str4el/homelogic/firmware/bus.c

/*
 * Copyright (C) 2013, 2014 Stephan Reinhard <Stephan-Reinhard@gmx.de>
 *
 * This file is part of Homelogic.
 *
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
 * You should have received a copy of the GNU General Public License
 * along with Homelogic.  If not, see <http://www.gnu.org/licenses/>.
 */

#include <ctype.h>
#include <string.h>
#include <stdio.h>
#include <stdlib.h>
#include <stdarg.h>
#include <stdbool.h>
#include <avr/eeprom.h>
#include <util/atomic.h>

#include "bus.h"
#include "usb.h"
#include "main.h"
#include "rtc.h"
#include "memory.h"
#include "prog.h"
#include "../common/timer.h"
#include "../common/counter.h"




bus_t bus = {
        .status = rx_start,

        .rx_buffer = "",
        .rx_len = 0,

        .tx_lock = 0,
        .tx_list = NULL,
};




const bus_command_table_t bus_command_table [] PROGMEM = {
        { "RESET", 5, bus_command_reset,          0,  0},
        { "IDY"  , 3, bus_command_identify,       0,  0},
        { "RUN"  , 3, bus_command_run,            0,  0},
        { "STOP" , 4, bus_command_stop,           0,  0},
        { "DEBUG", 5, bus_command_debug,          0,  0},
        { "STEP" , 4, bus_command_step,           0,  0},
        { "DUMP" , 4, bus_command_dump,           0,  0},
        { "PROG" , 4, bus_command_program,        8, BUS_DATA_MAX_LEN},
#ifdef RTC_SUPPORT
        { "SRTC" , 4, bus_command_set_rtc,       20, 20},
#endif
        { "SET"  , 3, bus_command_set_word,       8, 15},
        { "MEM"  , 3, bus_command_memory,         0,  0},
};





ISR(BUS_RXC_vect) {
        uint8_t in = BUS_UDR;

        switch (bus.status) {
        case rx_start:
                bus.rx_len = 0;
                bus.status = rx_ready;
        case rx_ready:
                if (bus.rx_len < BUS_BUFSIZE - 1) {
                        bus.rx_buffer[bus.rx_len] = in;
                        bus.rx_len++;
                }


                if (in == '\r') {
#ifdef USB_SUPPORT
                        usb_send_data(bus.rx_buffer, bus.rx_len);
#endif
                        bus.rx_buffer[bus.rx_len] = 0;
                        bus_command(bus.rx_buffer);
                        bus.rx_len = 0;
                }

                BUS_TX_LOCK(2 + adr * 2);
                break;

        case tx_start:
                bus.rx_len = 0;
                bus.status = tx_verify;
        case tx_verify:
                if (bus.rx_len < BUS_BUFSIZE) {
                        bus.rx_buffer[bus.rx_len] = in;
                        bus.rx_len++;
                }
                break;

        default:
                BUS_TX_LOCK(2 + adr * 2);
        }

}




void bus_init(void)
{
        ATOMIC_BLOCK(ATOMIC_RESTORESTATE) {
                SFR_SET(BUS_UCSZ0);
                SFR_SET(BUS_UCSZ1);
                SFR_SET(BUS_TXEN);
                SFR_SET(BUS_RXEN);
                SFR_SET(BUS_RXCIE);

                /* Aus einem mir absuolut räzelhaftem Grund funktioniert das Einstellen
                 * der Baudrate beim AtMega32 nur wenn es nach dem setzen der Flags passiert!
                 */
                BUS_UBRRH = UBRRH_VALUE;
                BUS_UBRRL = UBRRL_VALUE;
#if USE_2X
                SFR_SET(BUS_U2X);
#else
                SFR_CLR(BUS_U2X);
#endif
        }

        PIN_CLR(RE);
        BUS_TX_LOCK(2 + adr * 2);
}




void bus_transmit_data (const char * data, uint8_t len)
{
#ifdef USB_SUPPORT
        usb_send_data(data, (uint16_t) len);
#endif

        while (bus.tx_lock);
        bus.status = tx_start;
        PIN_SET(TE);


        for (uint8_t i = 0; i < len; i++) {
                while(SFR_IS_LOW(BUS_UDRE));
                BUS_UDR = data[i];
        }

        while (SFR_IS_LOW(BUS_TXC));
        SFR_SET(BUS_TXC);

        PIN_CLR(TE);
        BUS_TX_LOCK(2 + adr * 2);
        bus.status = rx_start;
}




bool bus_send_raw_sync(const char *data, uint8_t len)
{
        uint8_t count = 0;
        bus_transmit_data(data, len);
        while (!(len == bus.rx_len && memcmp(data, bus.rx_buffer, len) == 0)) {
                if (++count > BUS_MAX_RETRY) return false;
                bus_transmit_data(data, len);
        }
        return true;
}




bool bus_send_raw_async(const char *data, uint8_t len)
{
        bus_data_list_t *new = malloc(sizeof(*new) + len);
        if (!new) return false;

        new->next = NULL;
        new->len = len;
        memcpy(&new->data, data, len);

        if (bus.tx_list) {
                bus_data_list_t *last = bus.tx_list;
                while (last->next) last = last->next;
                last->next = new;
        } else {
                bus.tx_list = new;
        }

        return true;
}




void bus_flush_send_buffer()
{
        while (bus.tx_list) {
                bus_data_list_t *next = bus.tx_list->next;
                bus_send_raw_sync(&bus.tx_list->data, bus.tx_list->len);
                free(bus.tx_list);
                bus.tx_list = next;
        }
}




/* Erstellt eine Mitteilung im Standardformat und kopiert sie in den Sendepuffer
 */
bool bus_send_message_async(const char *cmd, uint8_t dst, const char *format, ...)
{
        char str[BUS_BUFSIZE];
        uint8_t len;

        len = snprintf(str, sizeof(str), "%s %02X %02X ", cmd, adr, dst);
        if (len >= sizeof(str) - 1) return false;

        if (format) {
                va_list args;
                va_start(args, format);
                len += vsnprintf(str + len, sizeof(str) - len, format, args);
                va_end(args);
                if (len >= sizeof(str) - 1) return false;
        }

        str[len] = '\r';
        return bus_send_raw_async(str, len + 1);
}




/* Erstellt eine Mitteilung im Standardformat und versendet sie
 */
bool bus_send_message_sync(const char *cmd, uint8_t dst, const char *format, ...)
{
        char str[BUS_BUFSIZE];
        uint8_t len;

        len = snprintf(str, sizeof(str), "%s %02X %02X ", cmd, adr, dst);
        if (len >= sizeof(str) - 1) return false;

        if (format) {
                va_list args;
                va_start(args, format);
                len += vsnprintf(str + len, sizeof(str) - len, format, args);
                va_end(args);
                if (len >= sizeof(str) - 1) return false;
        }

        str[len] = '\r';
        return bus_send_raw_sync(str, len + 1);
}




uint8_t bus_encode_prog_message(char *str, uint8_t len)
{
        snprintf(str, len, "VRY %02X FF %04X%02X", adr, prog_write.pos, prog_write.len);

        uint8_t pos = 0;

        for (uint8_t i = 0; i < prog_write.len; i++) {
                pos = strlen(str);
                snprintf(str + pos, len - pos, "%02X", prog_write.data[i]);
        }

        pos = strlen(str);
        str[pos++] = '\r';
        str[pos++] = 0;
        return pos;
}



/* Überprüft ob innerhalb der empangenen Zeichenkette ein Befehl aus
 * der bus_command_table gefunden wurde und die Nutzdaten die richtige
 * länge aufweisen.
 * Ist das der Fall wird die entsprechende Funktion aus der Tabelle
 * aufgerufen
 */
void bus_command(const char *str)
{
        char cmd[BUS_CMD_MAX_LEN + 1];
        char data[BUS_DATA_MAX_LEN + 1];
        unsigned char src;
        unsigned char dst;

        int ret = sscanf (str, "%" TOSTR(BUS_CMD_MAX_LEN) "s %2hhx %2hhx %" TOSTR(BUS_DATA_MAX_LEN) "s", cmd, &src, &dst, data);
        if (ret < 3) return;
        if (ret < 4) data[0] = 0;

        for (uint8_t i = 0; i < sizeof(bus_command_table) / sizeof(*bus_command_table); i++) {
                uint8_t command_len = pgm_read_byte(&bus_command_table[i].cmd_len);
                if (strncasecmp_P(cmd, bus_command_table[i].command, command_len) == 0) {
                        if (dst != adr && dst != 0xFF)return;

                        uint8_t min_data = pgm_read_byte(&bus_command_table[i].min_data);
                        uint8_t max_data = pgm_read_byte(&bus_command_table[i].max_data);

                        if (min_data > 0 && ret < 4) return;

                        uint8_t len = strlen(data);
                        if (!(min_data <= len && len <= max_data)) return;

                        bus_command_function_t function = (bus_command_function_t) pgm_read_word(&bus_command_table[i].function);
                        if (function) {
                                //bus_send_message_async("ACK", src, "%s %s", cmd, data);
                                function(src, data);
                        }
                        return;
                }
        }

}




void bus_command_reset (uint8_t sender, char *data)
{
        reset();
}




void bus_command_identify (uint8_t sender, char *data)
{
        bus_send_message_async("IDENT", sender, "%s", TOSTR(HARDWARE) " " TOSTR(MCU) " " VERSION);
}




void bus_command_run (uint8_t sender, char *data)
{
        state.coming = ps_run;
}




void bus_command_stop (uint8_t sender, char *data)
{
        state.coming = ps_stop;
}




void bus_command_debug (uint8_t sender, char *data)
{
        state.coming = ps_debug;
}




void bus_command_step (uint8_t sender, char *data)
{
        state.step = true;
}




void bus_command_dump (uint8_t sender, char *data)
{
        struct map_address_s am;
        char spec;

        for (uint16_t i = 0; i < progc.header.ph_address_map_size; i++) {
                eeprom_read_block(&am, (void *)(progc.header.ph_address_map_offset + i * sizeof(am)), sizeof(am));
                switch(am.ma_mem_adr & 0xE0) {
                case as_input: spec = 'I'; break;
                case as_output: spec = 'O'; break;
                case as_memory: spec = 'M'; break;

                case as_timer:
                        bus_send_message_async("INFO", sender, "%%T:%u.%u=%s", am.ma_device_adr, am.ma_mem_adr & 0x1F, TIMER_STATUS(progc.image[i]) ? "ON" : "OFF");
                        continue;

                case as_counter:
                        bus_send_message_async("INFO", sender, "%%C:%u.%u=%u", am.ma_device_adr, am.ma_mem_adr & 0x1F, COUNTER_VALUE(progc.image[i]));
                        continue;

                default: continue;
                }

                bus_send_message_async("INFO", sender, "%%%cW:%u.%u=%04X", spec, am.ma_device_adr, (am.ma_mem_adr & 0x1F) << 1, progc.image[i]);
        }


}




void bus_command_program (uint8_t sender, char *data)
{
        uint8_t len;
        if (sscanf(data, "%4hx%2hhx", (short unsigned int *)&prog_write.pos, &len) != 2) return;
        if (len > 10) return;

        data += 6;
        for (uint8_t i = 0; i < len; i++) {
                if (sscanf(data, "%2hhx", &prog_write.data[i]) != 1) return;
                data += 2;
        }

        prog_write.len = len;
}





#ifdef RTC_SUPPORT
void bus_command_set_rtc (uint8_t sender, char *data)
{
        rtc_time_t t;
        char day[2];

        if (sscanf(data, "%2c-%hhu.%hhu.%hhu-%hhu:%hhu:%hhu", day, &t.date, &t.month, &t.year, &t.hours, &t.minutes, &t.seconds) != 7) {
                return;
        }

        t.day     = rtc_daynum(day);
        if (t.day < 0) return;

        t.date    = rtc_bin2bcd(t.date);
        t.month   = rtc_bin2bcd(t.month);
        t.year    = rtc_bin2bcd(t.year);
        t.hours   = rtc_bin2bcd(t.hours);
        t.minutes = rtc_bin2bcd(t.minutes);
        t.seconds = rtc_bin2bcd(t.seconds);

        rtc_write_time(&t);
}
#endif




void bus_command_set_word (uint8_t sender, char *data)
{
        char str[4];
        uint8_t device;
        uint8_t byte;
        uint8_t spec;
        uint16_t value;


        if (!progc.valid) {
                return ;
        }

        if (sscanf(data, "%%T:%hhu.%hhu=%3s", &device, &byte, str) == 3) {
                if (byte >= 32) return;
                if (device == adr) return;

                spec = as_timer;
                int16_t n = prog_get_periphery_offset(device, spec, byte);
                if (n >= 0) {
                        progc.periphery[n] = ((str[1] == 'N') || (str[1] == 'n')) ? TIMER_STATUS_BIT : 0;
                }
                return;
        }

        if (sscanf(data, "%%C:%hhu.%hhu=%hu", &device, &byte, (short unsigned int *)&value) == 3) {
                if (byte >= 32) return;
                if (device == adr) return;

                spec = as_counter;
                int16_t n = prog_get_periphery_offset(device, spec, byte);
                if (n >= 0) {
                        progc.periphery[n] = value;
                }
                return;
        }

        if (sscanf(data, "%%%2s:%hhu.%hhu=%hx", str, &device, &byte, (short unsigned int *)&value) == 4) {
                if (byte >= 64) return;
                if (device == adr) return;

                if (str[1] == 'w' || str[1] == 'W') {
                        switch (str[0]) {
                        case 'i':
                        case 'I':
                                spec = as_input;
                                break;

                        case 'o':
                        case 'O':
                                spec = as_output;
                                break;
                        case 'm':
                        case 'M':
                                spec = as_memory;
                                break;
                        default:
                                return;
                        }

                        int16_t n = prog_get_periphery_offset(device, spec, byte);
                        if (n >= 0) {
                                progc.periphery[n] = value;
                        }
                }
                return;
        }

}




void bus_command_memory(uint8_t sender, char *data)
{
        bus_send_message_async("STACK", sender, "%ub", mem_used_stack());
        bus_send_message_async("HEAP" , sender, "%ub", mem_used_heap());
        bus_send_message_async("RAM"  , sender, "%ub", mem_free_ram());
}
