str4el/homelogic/firmware/i2c.c

/*
 * Copyright (C) 2013 - 2015 Stephan Reinhard <Stephan-Reinhard@gmx.de>
 *
 * This file is part of Homelogic.
 *
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
 * You should have received a copy of the GNU General Public License
 * along with Homelogic.  If not, see <http://www.gnu.org/licenses/>.
 */

#include "i2c.h"

int8_t i2c_write_byte(uint8_t data)
{
        int8_t ret;

        for (int8_t i = 7; i >= 0; i--) {
                _delay_us(I2C_T_HD_DAT);

                if (data & (1 << i)) {
                        PIN_OC_SET(SDA);
                } else {
                        PIN_OC_CLR(SDA);
                }

                _delay_us(I2C_T_LOW);
                PIN_OC_SET(SCL);
                _delay_us(I2C_T_HIGH);
                PIN_OC_CLR(SCL);
        }
        PIN_OC_SET(SDA);
        _delay_us(I2C_T_LOW);
        PIN_OC_SET(SCL);

        if (PIN_IS_HIGH(SDA)) {
                ret = -1;
        } else {
                ret = 0;
        }

        _delay_us(I2C_T_HIGH);
        PIN_OC_CLR(SCL);

        return ret;
}




uint8_t i2c_read_byte(uint8_t ack)
{
        uint8_t data = 0;

        PIN_OC_SET(SDA);

        for (int8_t i = 7; i >= 0; i--) {
                _delay_us(I2C_T_LOW);
                PIN_OC_SET(SCL);

                if (PIN_IS_HIGH(SDA)) {
                        data |= (1 << i);
                }

                _delay_us(I2C_T_HIGH);
                PIN_OC_CLR(SCL);
        }

        _delay_us(I2C_T_HD_DAT);

        if (ack) {
                PIN_OC_CLR(SDA);
        } else {
                PIN_OC_SET(SDA);
        }

        _delay_us(I2C_T_LOW);
        PIN_OC_SET(SCL);
        _delay_us(I2C_T_HIGH);
        PIN_OC_CLR(SCL);

        return data;
}




int8_t i2c_write(uint8_t sadr, void *data, uint8_t len)
{
        if (i2c_start()) {
                i2c_stop();
                return -1;
        }

        if (i2c_write_byte(sadr << 1)) {
                i2c_stop();
                return -2;
        }

        for (uint8_t i = 0; i < len; i++) {
                if (i2c_write_byte(((uint8_t *)data)[i])) {
                        i2c_stop();
                        return -3;
                }
        }

        i2c_stop();
        return 0;
}




int8_t i2c_pwrite(uint8_t sadr, uint8_t wadr , void *data, uint8_t len)
{
        if (i2c_start()) {
                i2c_stop();
                return -1;
        }

        if (i2c_write_byte(sadr << 1)) {
                i2c_stop();
                return -2;
        }

        if (i2c_write_byte(wadr)) {
                i2c_stop();
                return -3;
        }

        for (uint8_t i = 0; i < len; i++) {
                if (i2c_write_byte(((uint8_t *)data)[i])) {
                        i2c_stop();
                        return -4;
                }
        }

        i2c_stop();
        return 0;
}




int8_t i2c_read(uint8_t sadr, void *data, uint8_t len)
{
        if (i2c_start()) {
                i2c_stop();
                return -1;
        }

        if (i2c_write_byte((sadr << 1) | 1)) {
                i2c_stop();
                return -2;
        }

        for (uint8_t i = 0; i < len; i++) {
                ((uint8_t *)data)[i] = i2c_read_byte(i == (len - 1) ? I2C_NACK : I2C_ACK);
        }

        i2c_stop();
        return 0;
}




int8_t i2c_pread(uint8_t sadr, uint8_t wadr, void *data, uint8_t len)
{
        if (i2c_start()) {
                i2c_stop();
                return -1;
        }

        if (i2c_write_byte(sadr << 1)) {
                i2c_stop();
                return -2;
        }

        if (i2c_write_byte(wadr)) {
                i2c_stop();
                return -3;
        }

        if (i2c_start()) {
                i2c_stop();
                return -4;
        }

        if (i2c_write_byte((sadr << 1) | 1)) {
                i2c_stop();
                return -5;
        }

        for (uint8_t i = 0; i < len; i++) {
                ((uint8_t *)data)[i] = i2c_read_byte(i == (len - 1) ? I2C_NACK : I2C_ACK);
        }

        i2c_stop();
        return 0;
}
